Ssea2/R-aspirateur2000/doc/1.png

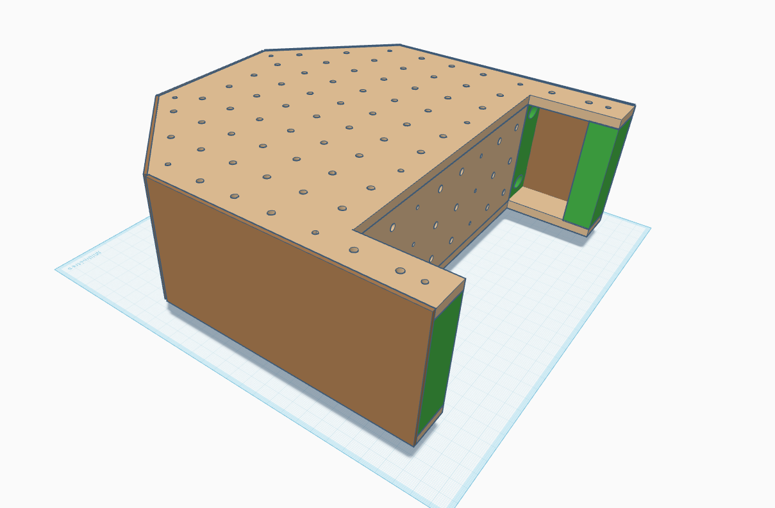
doc/1.png
