Ssea2/R-aspirateur2000/doc/2.png

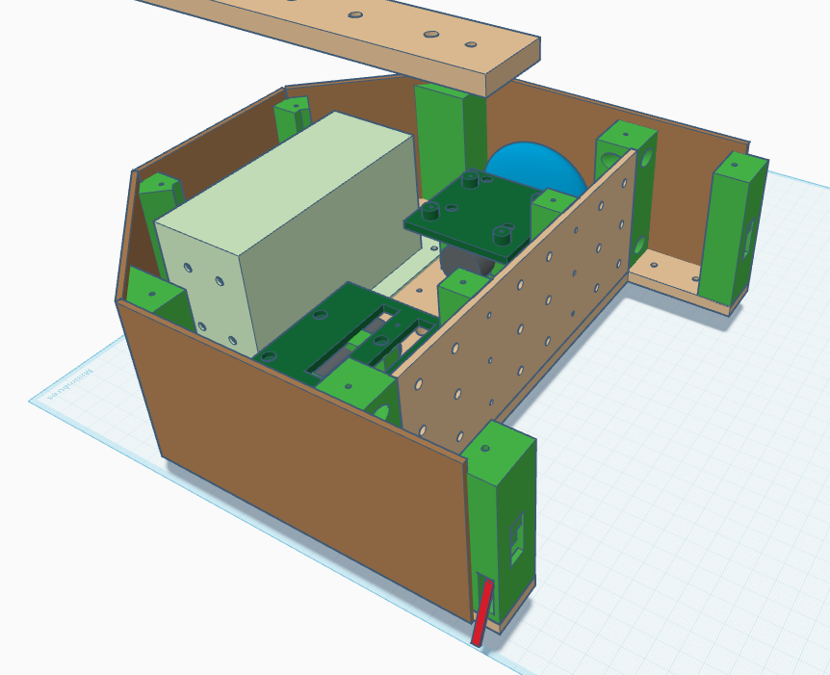
doc/2.png
